yu3ma/mikroAmpMeter/PCB_SCH/V15/PreviewV15-2-b.png

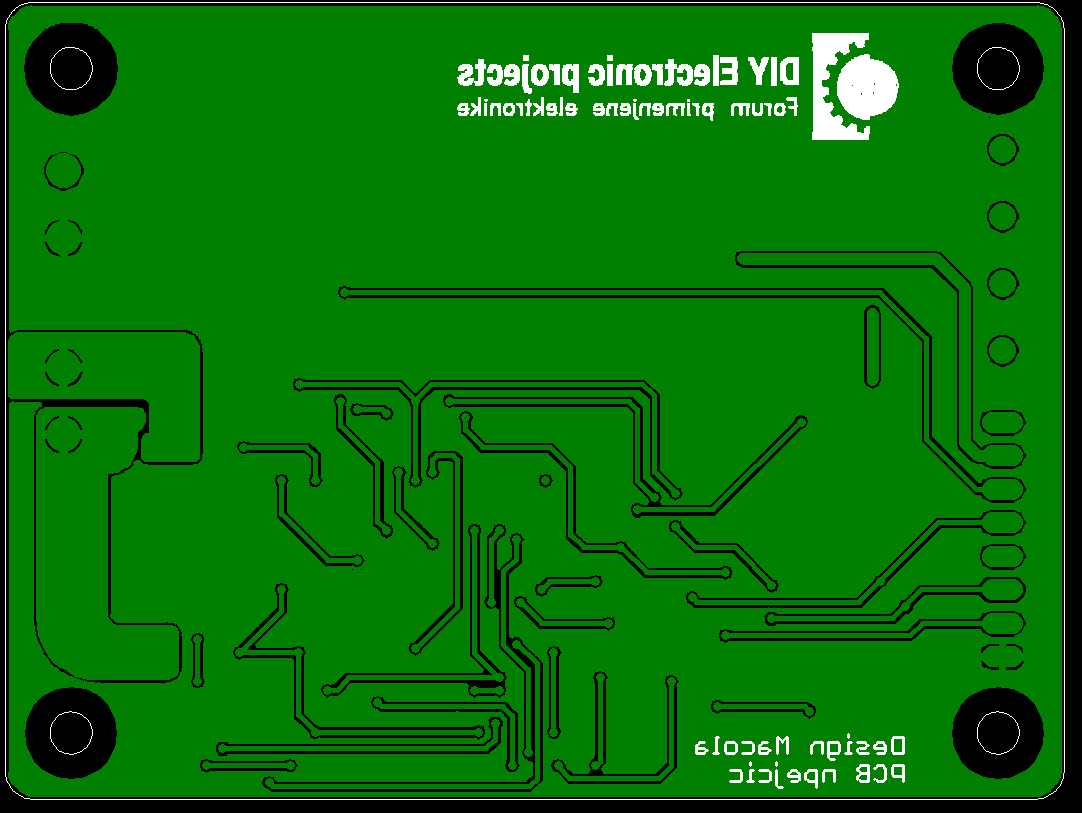
PCB_SCH/V15/PreviewV15-2-b.png
