yu3ma/mikroAmpMeter/PCB_SCH/V15/PreviewV15-2-t.png

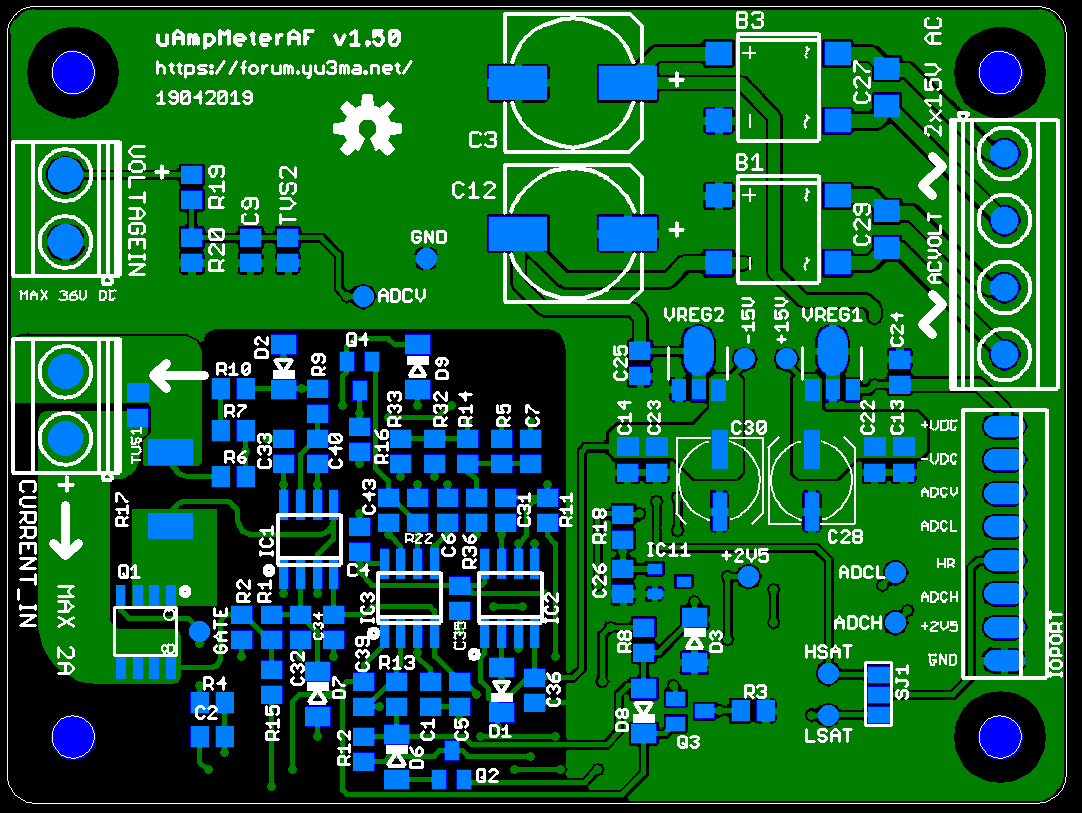
PCB_SCH/V15/PreviewV15-2-t.png
