yu3ma/mikroAmpMeter/Photos/02062019/IMG_20190602_175326.jpg

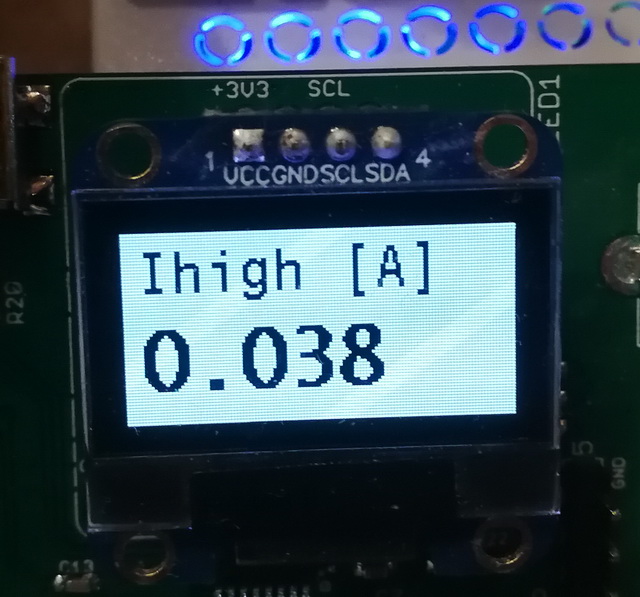
Photos/02062019/IMG_20190602_175326.jpg
