yu3ma/mikroAmpMeter/Photos/IMG_20190430_122912.jpg

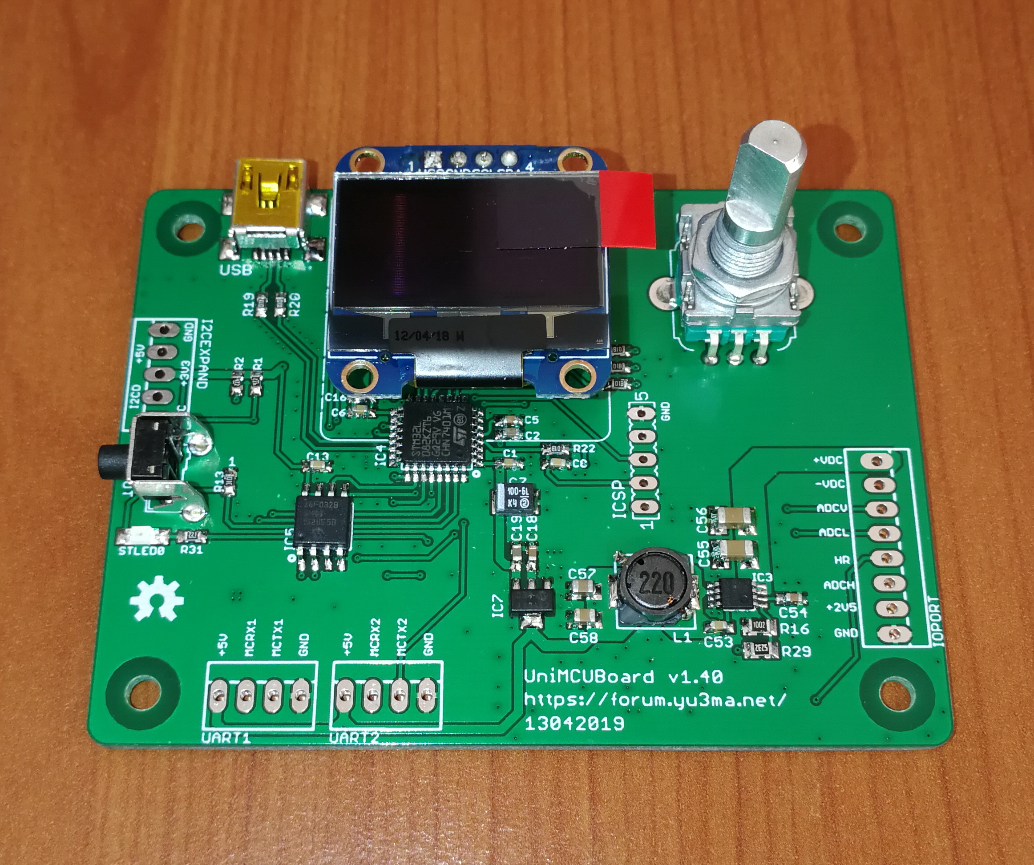
Photos/IMG_20190430_122912.jpg
