yu3ma/mikroAmpMeter/Photos/IMG_20190510_172400_Resize.jpg

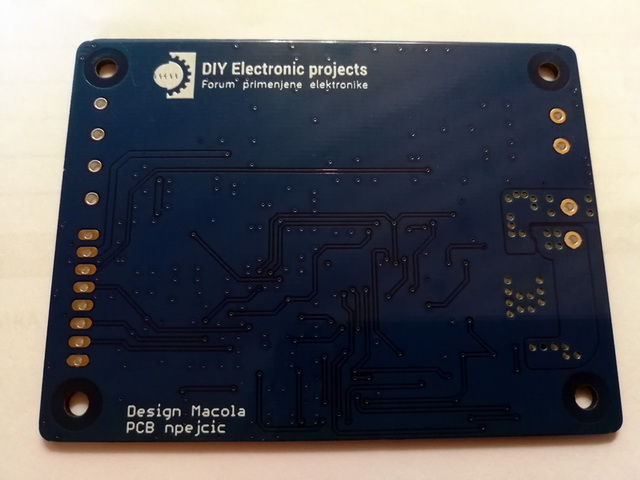
Photos/IMG_20190510_172400_Resize.jpg
