yu3ma/mikroAmpMeter/Photos/IMG_20190525_134637_Resize.jpg

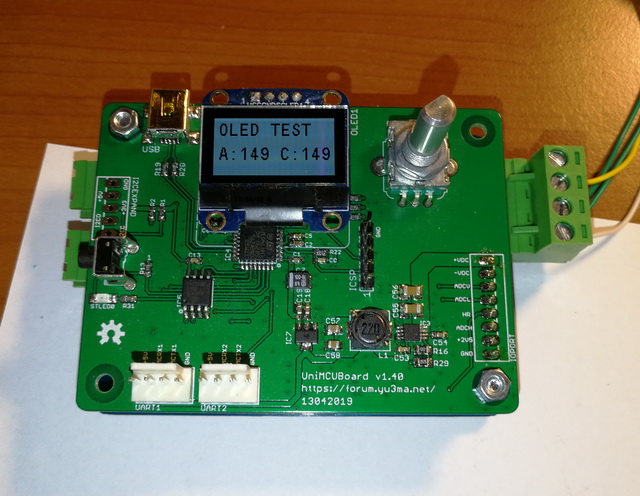
Photos/IMG_20190525_134637_Resize.jpg
