yu3ma/mikroAmpMeter/Photos/IMG_20190525_172200_Resize.jpg

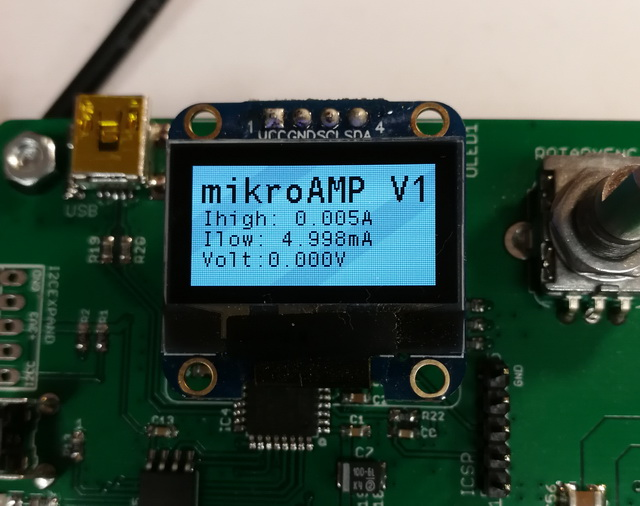
Photos/IMG_20190525_172200_Resize.jpg
