yu3ma/mikroAmpMeter/Photos/IMG_20190525_174938_Resize.jpg

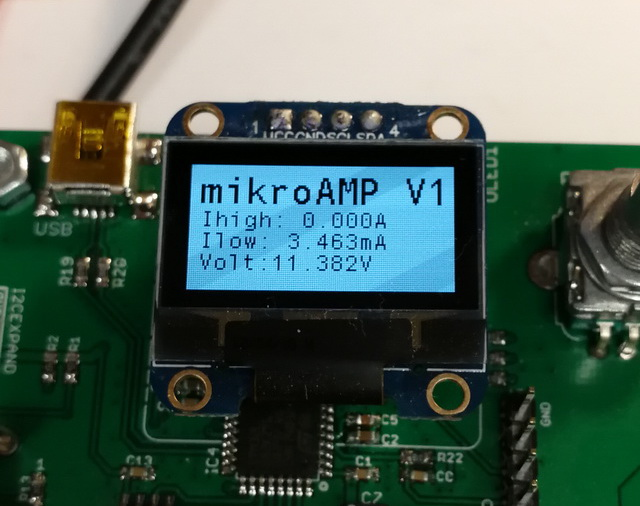
Photos/IMG_20190525_174938_Resize.jpg
