yu3ma/mikroAmpMeter/Simulation/MACOLA LOW -HIGH AUTO RANGE VER2.0.JPG

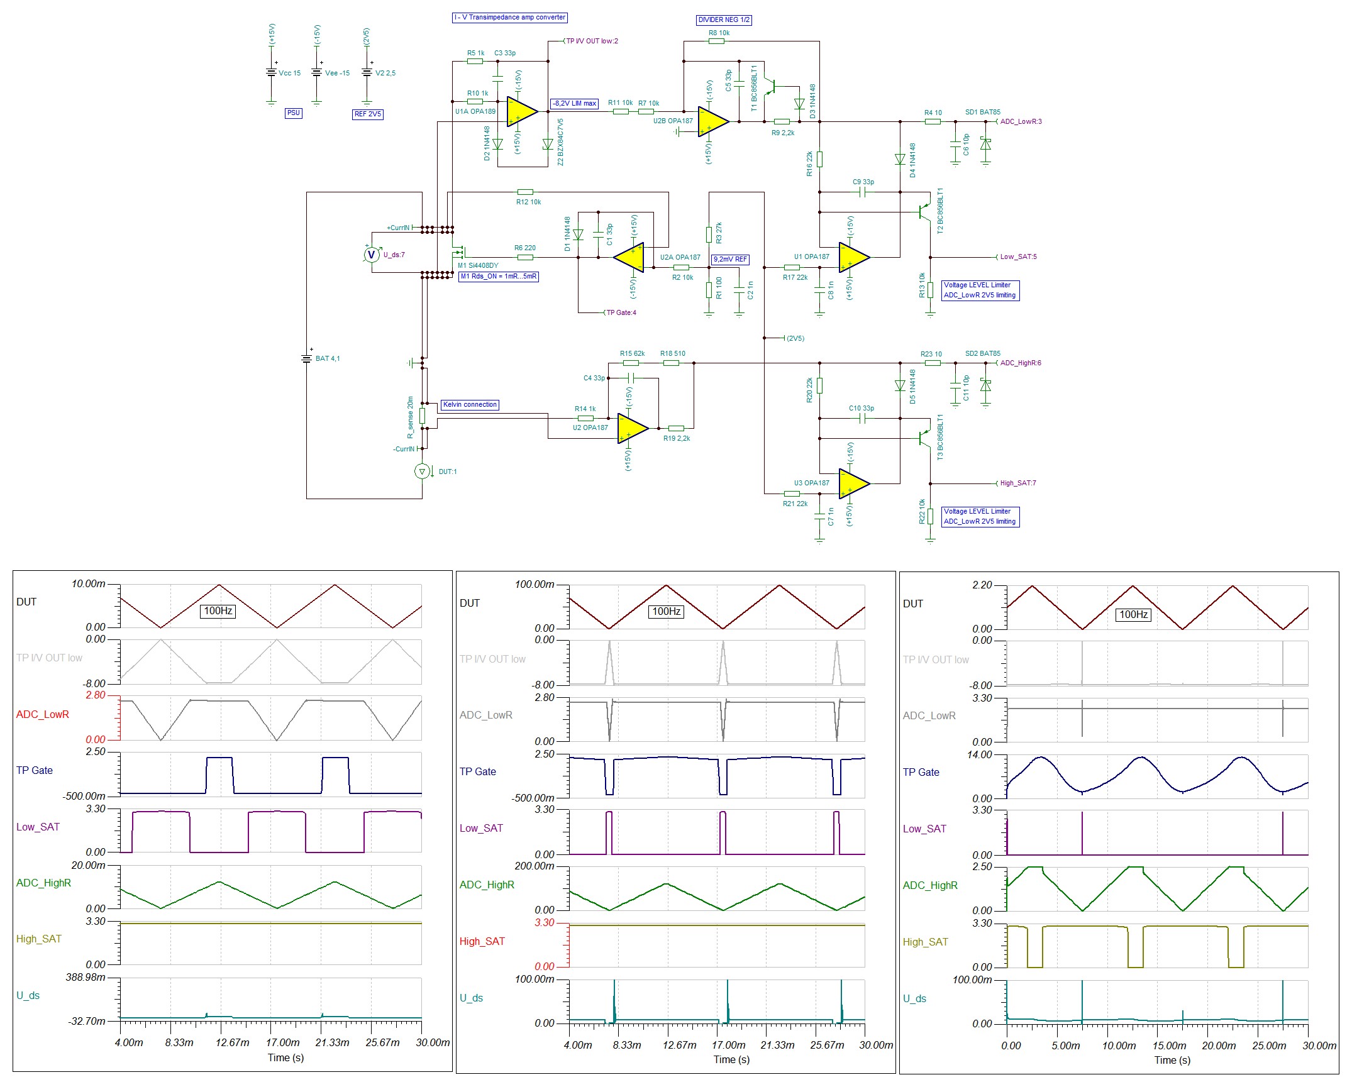
Simulation/MACOLA LOW -HIGH AUTO RANGE VER2.0.JPG
