yu3ma/mikroAmpMeter/Simulation/2range_curr_2.asc

C1: cap; 100p
C2: cap; 10n
C3: cap; 33p
C5: cap; 33p
C6: cap; 10p
D1: diode; 1N4148
D2: LED; NSCW100
D3: LED; NSCW100
D4: zener; 1N750
D5: schottky; BAT54
D6: schottky; BAT54
M1: nmos; IRF6609
Q1: npn; BC817-25
Q2: pnp; BC807-25
R1: res; 0.02R
R2: res; 1K0
R3: res; 4K7
R4: res; 22R
R5: res; 2K2
R6: res; 1K0
R7: res; 62K
R8: res; 2K2
R9: res; 2K2
R10: res; 510R0
R11: res; 20K0
R12: res; 10K0
R13: res; 2K7
R14: res; 22K
R15: res; 2k2
R16: res; 1K8
R17: res; 4K7
R18: res; 2K2
R19: res; 22K
R20: res; 22K
U1: LT1022A
U2: LT1022A
U3: LT1022A
U4: LT1022A
U5: LT1022A
U6: LT1022A
U7: LT1004-2.5
U8: LT1004-2.5
U9: LT1004-2.5
V1: voltage; 15.0V
V2: voltage; 15.0V
Named nets: 0, Vcc, Vee, ADC_lowR, ADC_highR, HIGH_range, +2.5, +Curr_in, -Curr_out, -5
5mA=2V50
2A=2V50
4V7
h_lev=3V3
l_satur.
h_satur.
